heolfief/VU-meter/docs/data__structure_8h__dep__incl.png

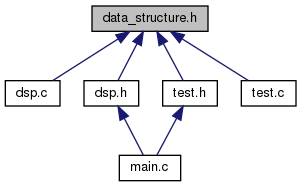
docs/data__structure_8h__dep__incl.png
