heolfief/VU-meter/docs/dsp_8c__incl.png

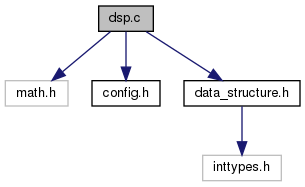
docs/dsp_8c__incl.png
