heolfief/VU-meter/docs/dsp_8h__incl.png

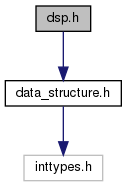
docs/dsp_8h__incl.png
