heolfief/VU-meter/docs/hc595_8c__incl.png

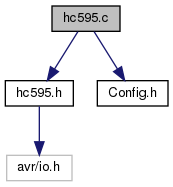
docs/hc595_8c__incl.png
