heolfief/VU-meter/docs/img/_MG_8801-Modifier.jpg

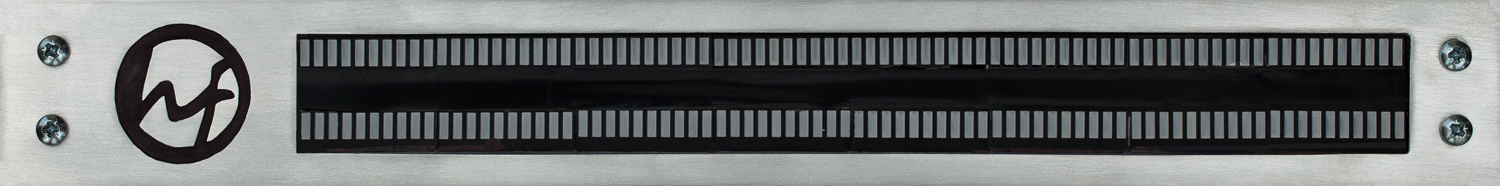
docs/img/_MG_8801-Modifier.jpg
