heolfief/VU-meter/docs/img/_MG_8803-Modifier.jpg

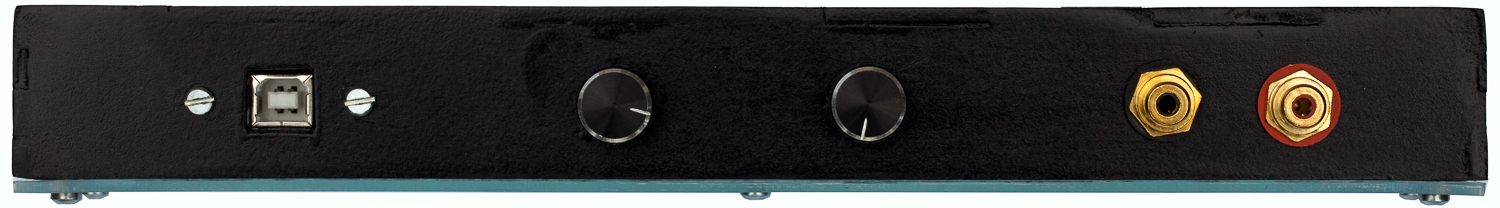
docs/img/_MG_8803-Modifier.jpg
