heolfief/VU-meter/docs/main_8c__incl.png

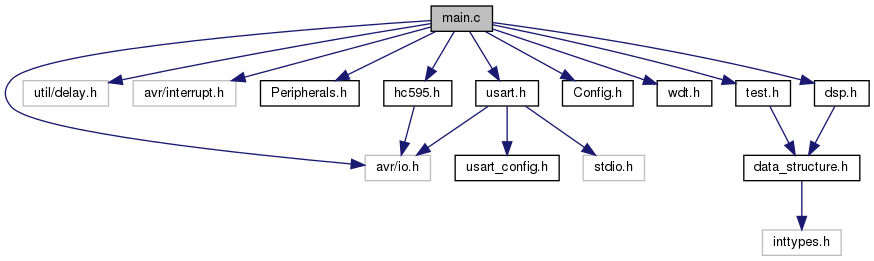
docs/main_8c__incl.png
