heolfief/VU-meter/docs/peripherals_8c__incl.png

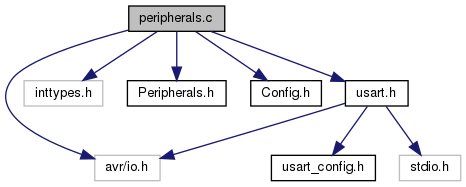
docs/peripherals_8c__incl.png
