heolfief/VU-meter/docs/usart_8c__incl.png

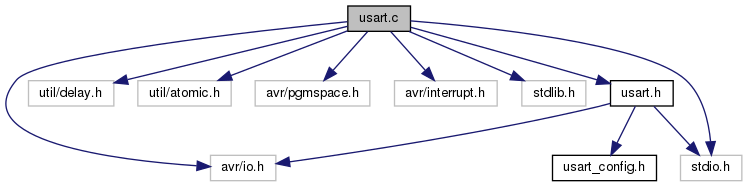
docs/usart_8c__incl.png
