heolfief/VU-meter/docs/usart__config_8h__dep__incl.png

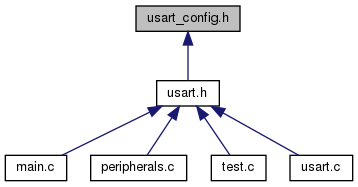
docs/usart__config_8h__dep__incl.png
