heolfief/VU-meter/Hardware/Simulation/LTSPICE Simulation.asc

C1: cap; 22n
C2: cap; 100n
D1: diode; 1N914
D2: diode; 1N914
R1: res; 100k
R2: res; 100k
R3: res; 100k
R4: res; 100k
R5: res; 100k
R6: res; 47k
R8: res; 24k
U1: UniversalOpamp2
U2: UniversalOpamp2
U4: UniversalOpamp2
V1: voltage; wavefile=audiosample.wav
V2: voltage; 2.5
Named nets: 0, Vin, Vrect, VCC, Vfilt
.tran 0 3 0
Sallen-Key Low-pass Filter
fc = 10Hz
Q = 1
Damping ratio = 0.5
Precision full wave rectifier
